atheros/backtothefuture-clock/eagle/month-led-r1.brd

## EAGLE design eagle/month-led-r1.brd (2014-04-21)

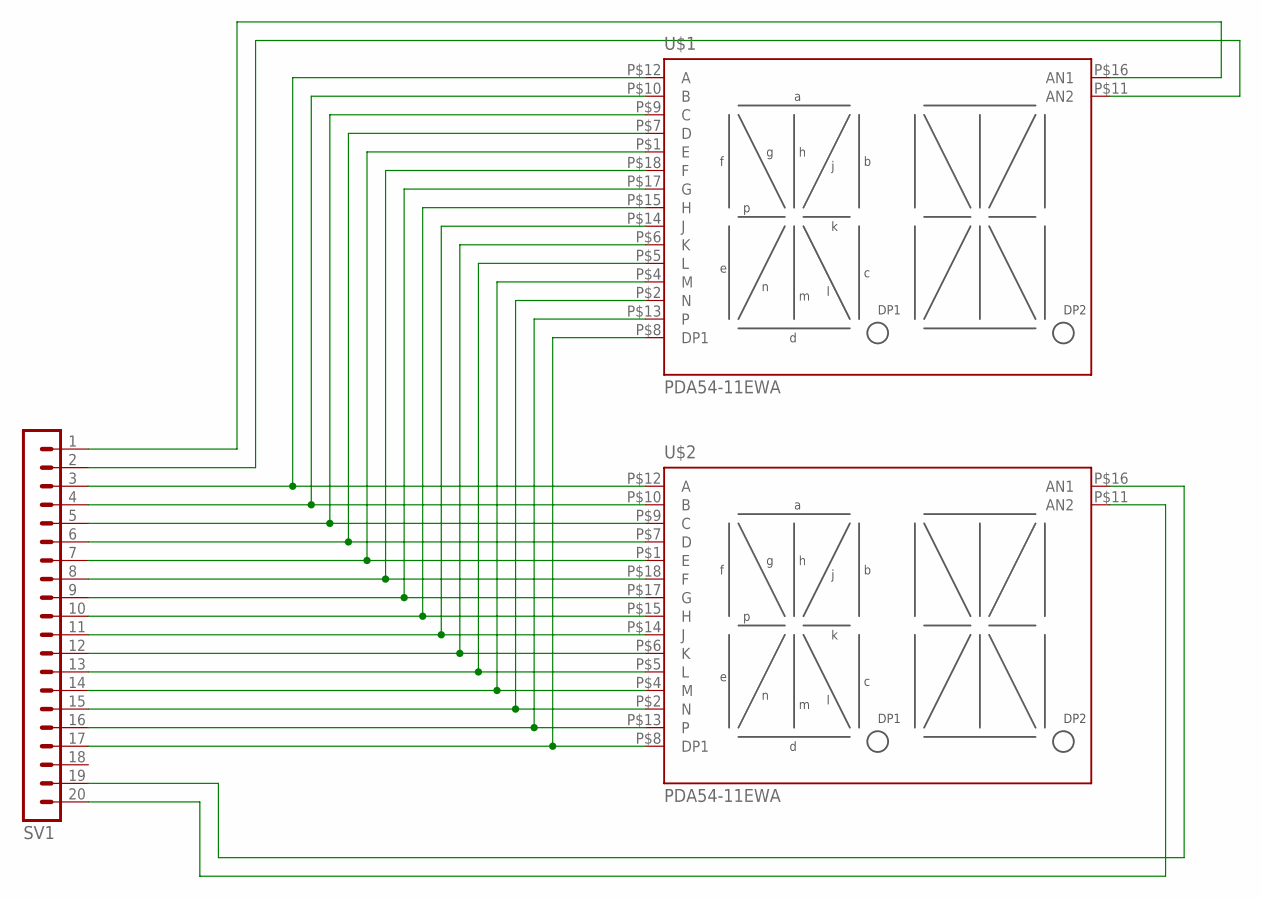
[picture p19: schematic month-led-r1.sch]

Parts:
SV1: MA20-1W
U$1, U$2: PDA54-11EWA; PDA54-11XX

Connections:
unnamed: SV1.3, U$1.P$12 (A), U$2.P$12 (A)
unnamed: SV1.4, U$1.P$10 (B), U$2.P$10 (B)
unnamed: SV1.5, U$1.P$9 (C), U$2.P$9 (C)
unnamed: SV1.6, U$1.P$7 (D), U$2.P$7 (D)
unnamed: SV1.7, U$1.P$1 (E), U$2.P$1 (E)
unnamed: SV1.8, U$1.P$18 (F), U$2.P$18 (F)
unnamed: SV1.9, U$1.P$17 (G), U$2.P$17 (G)
unnamed: SV1.10, U$1.P$15 (H), U$2.P$15 (H)
unnamed: SV1.11, U$1.P$14 (J), U$2.P$14 (J)
unnamed: SV1.12, U$1.P$6 (K), U$2.P$6 (K)
unnamed: SV1.13, U$1.P$5 (L), U$2.P$5 (L)
unnamed: SV1.14, U$1.P$4 (M), U$2.P$4 (M)
unnamed: SV1.15, U$1.P$2 (N), U$2.P$2 (N)
unnamed: SV1.16, U$1.P$13, U$2.P$13
unnamed: SV1.17, U$1.P$8 (DP1), U$2.P$8 (DP1)
unnamed: SV1.2, U$1.P$11 (AN2)
unnamed: SV1.19, U$2.P$16 (AN1)
unnamed: SV1.20, U$2.P$11 (AN2)
unnamed: SV1.1, U$1.P$16 (AN1)

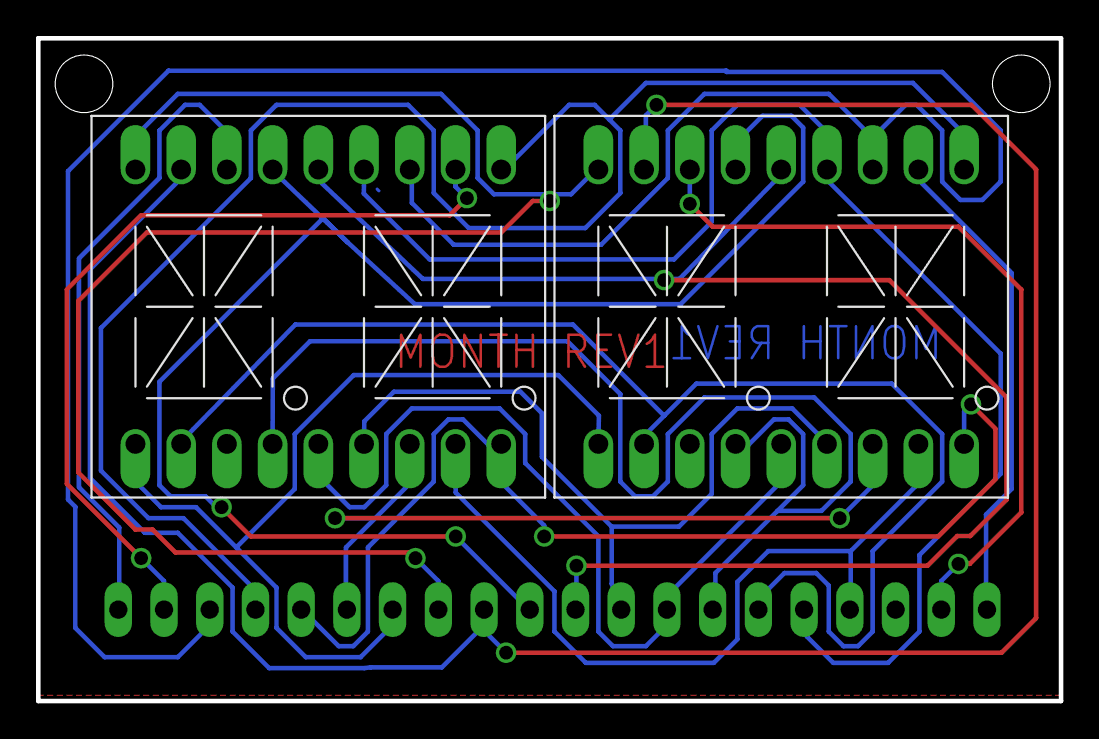
[picture p20: board month-led-r1.brd from above]

Board: 2 copper layers, 56.8 x 36.8 mm, 3 parts (1 on the bottom side), 19 nets.
